woeps/pico-genseq/data/midi-trs-a.png

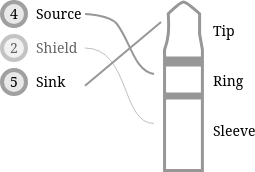
data/midi-trs-a.png
