woeps/pico-genseq/data/midi-trs-b.png

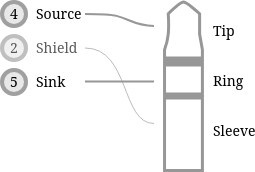
data/midi-trs-b.png
