woeps/pico-genseq/src/ui/hardware/Led.cpp

#include "Led.h"
#include "pico/stdlib.h"
#include "hardware/gpio.h"

namespace hardware {

Led::Led(uint8_t pin) :
    pin(pin),
    state(false),
    blinking(false),
    onTime(0),
    offTime(0),
    lastToggleTime(0)
{
    gpio_init(pin);
    gpio_set_dir(pin, GPIO_OUT);
    off();
}


void Led::on()
{
    gpio_put(pin, 1);
    state = true;
    blinking = false;
}

void Led::off()
{
    gpio_put(pin, 0);
    state = false;
    blinking = false;
}

void Led::toggle()
{
    state = !state;
    gpio_put(pin, state);
}

void Led::blink(uint32_t onTime, uint32_t offTime)
{
    this->onTime = onTime;
    this->offTime = offTime;
    this->blinking = true;
    lastToggleTime = to_ms_since_boot(get_absolute_time());
    gpio_put(pin, 1);
    this->state = true;
}

void Led::update()
{
    if (!blinking) return;

    uint32_t currentTime = to_ms_since_boot(get_absolute_time());
    uint32_t elapsed = currentTime - lastToggleTime;

    if ((state && elapsed >= onTime) || (!state && elapsed >= offTime)) {
        toggle();
        lastToggleTime = currentTime;
    }
}

} // namespace hardware
